yesimon/datagoo/docs/images/case_cad_transparent.png

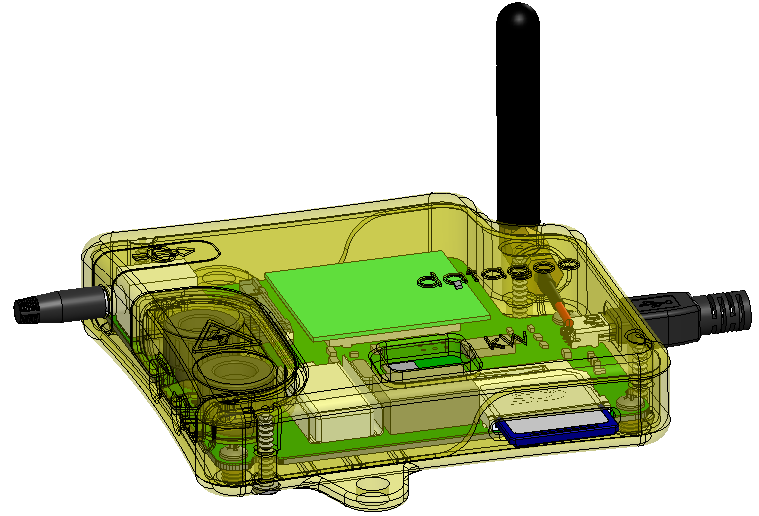
docs/images/case_cad_transparent.png
